lucky01/PIN2DMD/hardware/DE 128x16 CONTROLLER/README.md

# PIN2DMD - 128x16 DOT MATRIX CONTROLLER BOARD

This are the PCB files for the Dot Matrix Contoller Board like used in early Data East machines 
e.g Batman, Checkpoint, Hook, Star Trek 25th anniversary and Teenage Mutant Ninja Turtles. It is needed to connect these
machines to the PIN2DMD Nucleo shield. PCB design by Rappelbox, UncleSash and Lucky1
