lucky01/PIN2DMD/firmware/latest/README.md

# PIN2DMD

Here you find the latest firmware for EVO128x32, EVO128x16, EVO192x64 and EVO256x64 boards. 

Latest generation STM32F429ZI NUCLEO-144 boards use the firmware in the V4 Nucleo-144 folder. 

Older deprecated STM32F407 Discovery and custom controller hardware boards use the firmware in the V3 STM32F4 Discovery folder

Custom hardware based XL firmware for SEGA192x64 displays is in the Custom_XL folder.
