lucky01/PIN2DMD/tools/sample_files/README.md

# PIN2DMD TOOL SAMPLE FILES

pin2dmd.pal - Amber palette file. Just copy to your SD card to get a plasma like look.
boot.fsq - short video sequence showing at startup of the device if copied to the SD.
