lucky01/PIN2DMD/integration/XDMD/readme.md

These dlls replace the existing dlls of xdmd applications like PinballX and UltraDMD and create a device independant dmddevice.dll driver interface.
You also need to copy the dmddevice.dll driver to the same directory to make it work with your display.
