lucky01/PIN2DMD/integration/Spooky Pinball/README.md

# Modified parallax propeller code for Spooky Pinball`s Americas Most Haunted

Replace the PROP_023.BIN in DMD folder of AMH_SD_V023.zip update image. Update your firmware
according to official instructions.

This modification works with pin2dmd (and the original X-Pin display of course :-)
