lucky01/PIN2DMD/firmware/latest/SYSXDMD/README.md

# SYSXDMD

Firmware for PIN2MD SysXDmd controller board .

Use the .dfu file with the DfuSEDemo Utility to upload the firmware to your device
using the user USB port in dfu mode.
http://www.st.com/en/development-tools/stsw-stm32080.html

For information how to get a activation key for your device 
please visit http://www.pin2dmd.com
