lucky01/PIN2DMD/firmware/latest/EVO128x32_EVO128x16/README.md

# PIN2DMD

Firmware for a EVO128x32 and EVO 128x16 board to drive a HUB75 RGB panel.

Standard firmware is for two 64x32 1/16 scan P2.5 panels in a row for 128x32 resolution.

Copy the .upd file to you micro SD card to upload the firmware to your device with
firmware >= 2.50 preinstalled. (for XL >= 2.08) 

Use the .bin file with the ST-Link Utility to upload the firmware to your device
using the ST-Link interface
http://www.st.com/web/en/catalog/tools/PF258168

Use the .dfu file with the DfuSEDemo Utility to upload the firmware to your device
using the user USB port in dfu mode.
http://www.st.com/en/development-tools/stsw-stm32080.html

For information how to get a activation key for your device 
please visit http://www.pin2dmd.com
