lucky01/PIN2DMD/firmware/latest/CUSTOM_XL/README.md

# PIN2DMD

Firmware for custom PIN2DMD-XL controller board from GGS.

XL firmware is for three 64x64 1/32 scan panels in a row for 192x64 resolution.(SEGA)

Copy the .upd file to you micro SD card to upload the firmware to your device with
firmware >= 2.50 preinstalled. (for XL >= 2.08) 

Use the .bin file with the ST-Link Utility to upload the firmware to your device
using the ST-Link interface
http://www.st.com/web/en/catalog/tools/PF258168

For information how to get a activation key for your device 
please visit http://www.pin2dmd.com
